jgordo32/nrf24_andretti/Wireless Controller Case/Renderings/final1.png

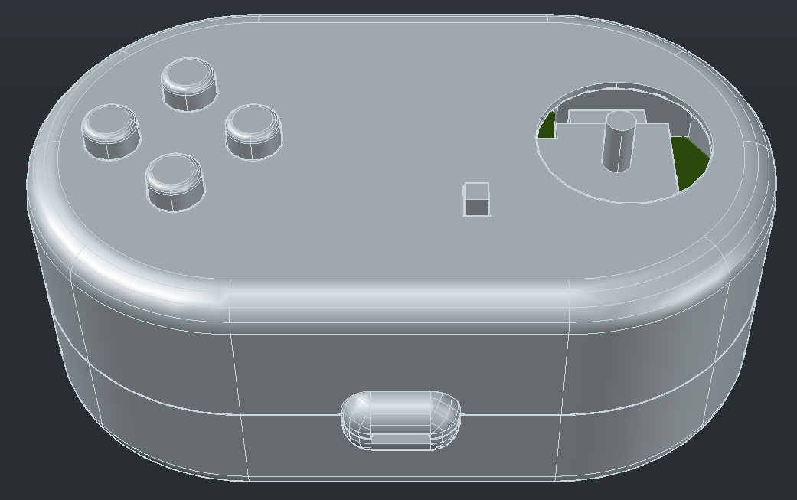
Wireless Controller Case/Renderings/final1.png
