jgordo32/nrf24_andretti/Wireless Controller Case/Renderings/board_components.png

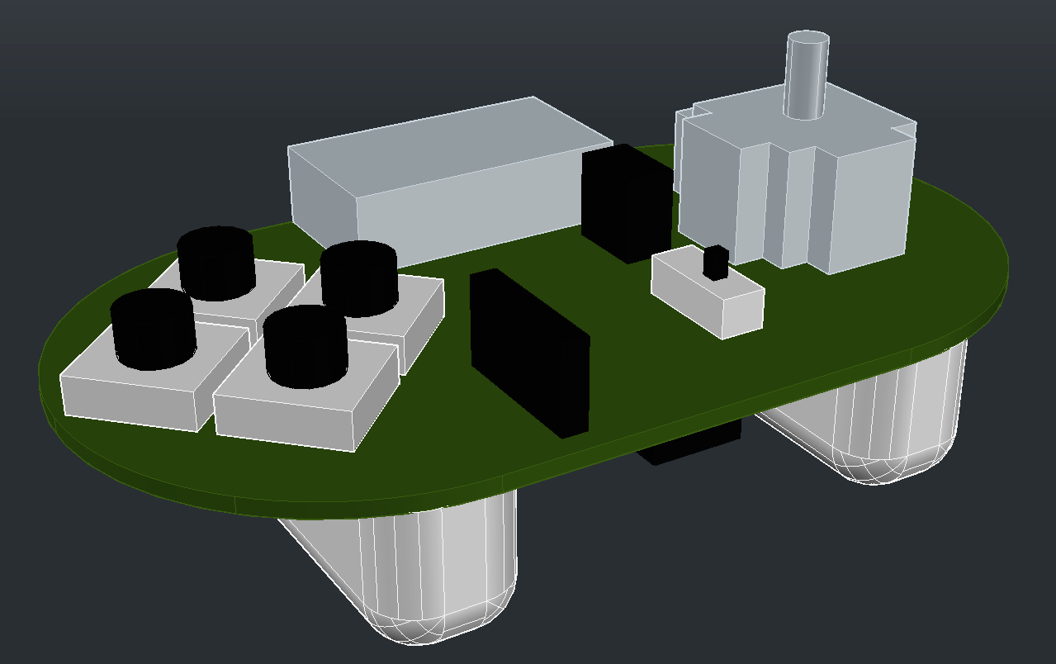
Wireless Controller Case/Renderings/board_components.png
