jgordo32/nrf24_andretti/DREAMERv4_games/ArduinoGame.h

#ifndef _ARDUINO_GAME_H_
#define _ARDUINO_GAME_H_

#define BOARD_SIZE  16 /* In pixels */
#define IRQ_HZ      32

#define X 0
#define Y 1

#define WRAP(x,y) ( ((x) < 0) ? ((x) + (y)) : ( ((x) >= (y)) ? ((x) - (y)) : (x) ) )
#define CLAMP(x,y) ((x) > (y) ? (y) : ((x) < 0 ? 0 : (x)))

// Pins!

#define P1_X 1 // Analog
#define P1_Y 2 // Analog
#define P1_BD 8 // Digital
#define P1_BL 9 // Digital
#define P1_BR 10 // Digital
#define P1_BU 11 // Digital

#define P2_X 0 // Analog
#define P2_Y 11 // Analog, same as D12
#define P2_BU 0 // Digital
#define P2_BR 1 // Digital
#define P2_BL 4 // Digital
#define P2_BD 5 // Digital

#define RANDOM_PIN   3  // Analog, not connected

/*
 * Lookup tables!
 */
static const signed char cos32[360] = {
  32, 32, 32, 32, 32, 32, 32, 32, 32, 32, 32, 31, 31, 31, 31, 31, 31, 31, 30, 30, 30, 30, 30, 29, 29, 29, 29, 29, 28, 28, 28,
  27, 27, 27, 27, 26, 26, 26, 25, 25, 25, 24, 24, 23, 23, 23, 22, 22, 21, 21, 21, 20, 20, 19, 19, 18, 18, 17, 17, 16, 16, 16, 15, 15, 14, 14, 13, 13, 12,
  11, 11, 10, 10, 9, 9, 8, 8, 7, 7, 6, 6, 5, 4, 4, 3, 3, 2, 2, 1, 1, 0, -1, -1, -2, -2, -3, -3, -4, -4, -5, -6, -6, -7, -7, -8, -8, -9, -9, -10, -10, -11,
  -11, -12, -13, -13, -14, -14, -15, -15, -16, -16, -16, -17, -17, -18, -18, -19, -19, -20, -20, -21, -21, -21, -22, -22, -23, -23, -23, -24, -24, -25,
  -25, -25, -26, -26, -26, -27, -27, -27, -27, -28, -28, -28, -29, -29, -29, -29, -29, -30, -30, -30, -30, -30, -31, -31, -31, -31, -31, -31, -31, -32,
  -32, -32, -32, -32, -32, -32, -32, -32, -32, -32, -32, -32, -32, -32, -32, -32, -32, -32, -32, -32, -31, -31, -31, -31, -31, -31, -31, -30, -30, -30,
  -30, -30, -29, -29, -29, -29, -29, -28, -28, -28, -27, -27, -27, -27, -26, -26, -26, -25, -25, -25, -24, -24, -23, -23, -23, -22, -22, -21, -21, -21,
  -20, -20, -19, -19, -18, -18, -17, -17, -16, -16, -16, -15, -15, -14, -14, -13, -13, -12, -11, -11, -10, -10, -9, -9, -8, -8, -7, -7, -6, -6, -5, -4,
  -4, -3, -3, -2, -2, -1, -1, 0, 1, 1, 2, 2, 3, 3, 4, 4, 5, 6, 6, 7, 7, 8, 8, 9, 9, 10, 10, 11, 11, 12, 13, 13, 14, 14, 15, 15, 16, 16, 16, 17, 17, 18,
  18, 19, 19, 20, 20, 21, 21, 21, 22, 22, 23, 23, 23, 24, 24, 25, 25, 25, 26, 26, 26, 27, 27, 27, 27, 28, 28, 28, 29, 29, 29, 29, 29, 30, 30, 30, 30, 30,
  31, 31, 31, 31, 31, 31, 31, 32, 32, 32, 32, 32, 32, 32, 32, 32, 32
};
static const signed char sin32[360] = {
  0, 1, 1, 2, 2, 3, 3, 4, 4, 5, 6, 6, 7, 7, 8, 8, 9, 9, 10, 10, 11, 11, 12, 13, 13, 14, 14, 15, 15, 16, 16, 16, 17, 17, 18, 18,
  19, 19, 20, 20, 21, 21, 21, 22, 22, 23, 23, 23, 24, 24, 25, 25, 25, 26, 26, 26, 27, 27, 27, 27, 28, 28, 28, 29, 29, 29, 29, 29, 30, 30, 30, 30, 30, 31,
  31, 31, 31, 31, 31, 31, 32, 32, 32, 32, 32, 32, 32, 32, 32, 32, 32, 32, 32, 32, 32, 32, 32, 32, 32, 32, 32, 31, 31, 31, 31, 31, 31, 31, 30, 30, 30, 30,
  30, 29, 29, 29, 29, 29, 28, 28, 28, 27, 27, 27, 27, 26, 26, 26, 25, 25, 25, 24, 24, 23, 23, 23, 22, 22, 21, 21, 21, 20, 20, 19, 19, 18, 18, 17, 17, 16,
  16, 16, 15, 15, 14, 14, 13, 13, 12, 11, 11, 10, 10, 9, 9, 8, 8, 7, 7, 6, 6, 5, 4, 4, 3, 3, 2, 2, 1, 1, 0, -1, -1, -2, -2, -3, -3, -4, -4, -5, -6, -6,
  -7, -7, -8, -8, -9, -9, -10, -10, -11, -11, -12, -13, -13, -14, -14, -15, -15, -16, -16, -16, -17, -17, -18, -18, -19, -19, -20, -20, -21, -21, -21,
  -22, -22, -23, -23, -23, -24, -24, -25, -25, -25, -26, -26, -26, -27, -27, -27, -27, -28, -28, -28, -29, -29, -29, -29, -29, -30, -30, -30, -30, -30,
  -31, -31, -31, -31, -31, -31, -31, -32, -32, -32, -32, -32, -32, -32, -32, -32, -32, -32, -32, -32, -32, -32, -32, -32, -32, -32, -32, -32, -31, -31,
  -31, -31, -31, -31, -31, -30, -30, -30, -30, -30, -29, -29, -29, -29, -29, -28, -28, -28, -27, -27, -27, -27, -26, -26, -26, -25, -25, -25, -24, -24,
  -23, -23, -23, -22, -22, -21, -21, -21, -20, -20, -19, -19, -18, -18, -17, -17, -16, -16, -16, -15, -15, -14, -14, -13, -13, -12, -11, -11, -10, -10,
  -9, -9, -8, -8, -7, -7, -6, -6, -5, -4, -4, -3, -3, -2, -2, -1, -1
};

class ArduinoGame
{
public:
  ArduinoGame() {};
  ~ArduinoGame() {};
  virtual void UpdatePhysics(volatile unsigned char field[BOARD_SIZE][BOARD_SIZE]) = 0;
  virtual void ResetGame(volatile unsigned char field[BOARD_SIZE][BOARD_SIZE], unsigned char isInit, unsigned char whoWon) = 0;
  virtual void ProcessInput(volatile unsigned char field[BOARD_SIZE][BOARD_SIZE], long p1ax, long p1ay, char p1b0, char p1b1, char p1b2, char p1b3, long p2ax, long p2ay, char p2b0, char p2b1, char p2b2, char p2b3) = 0;
};

#endif
